neuromorphic-paris/hibiscus/parts/box/ethernet.stl

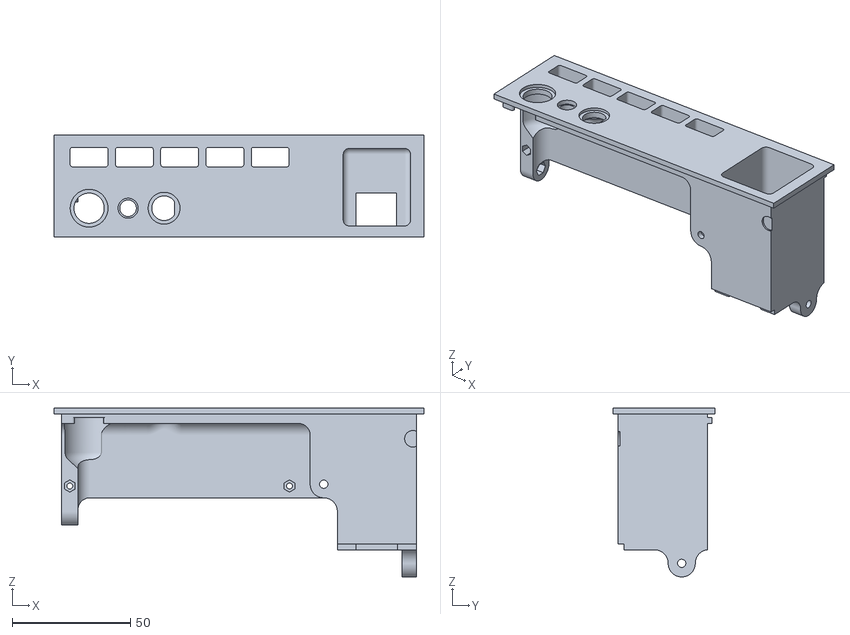
[picture p18: CAD file, 2019-12-23]
parts/box/ethernet.stl
156.7 x 43.2 x 71.5
