neuromorphic-paris/hibiscus/parts/box/slider.stl

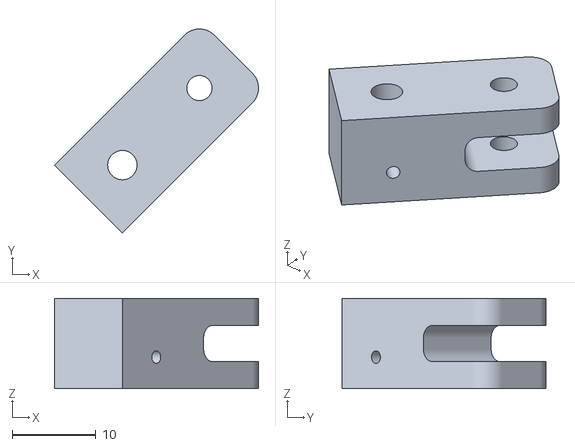
[picture p19: CAD file, 2019-12-23]
parts/box/slider.stl
24.3 x 24.3 x 10.7
