neuromorphic-paris/hibiscus/parts/box/antenna_spacer.stl

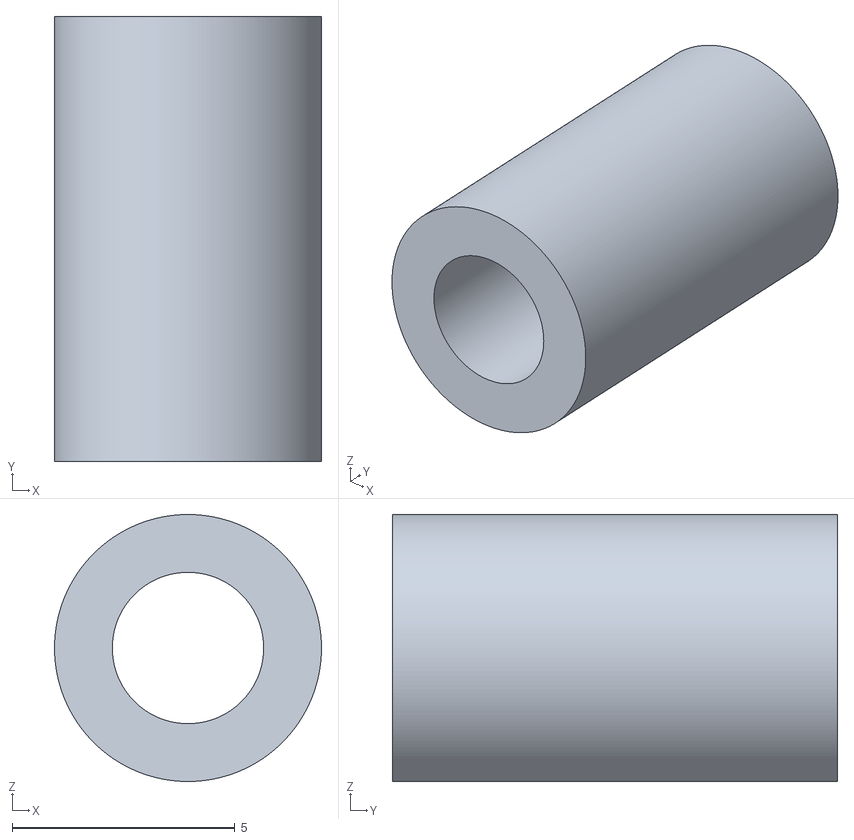
[picture p20: CAD file, 2019-12-23]
parts/box/antenna_spacer.stl
6.00 x 10.0 x 6.00
