neuromorphic-paris/hibiscus/parts/box/chassis.stl

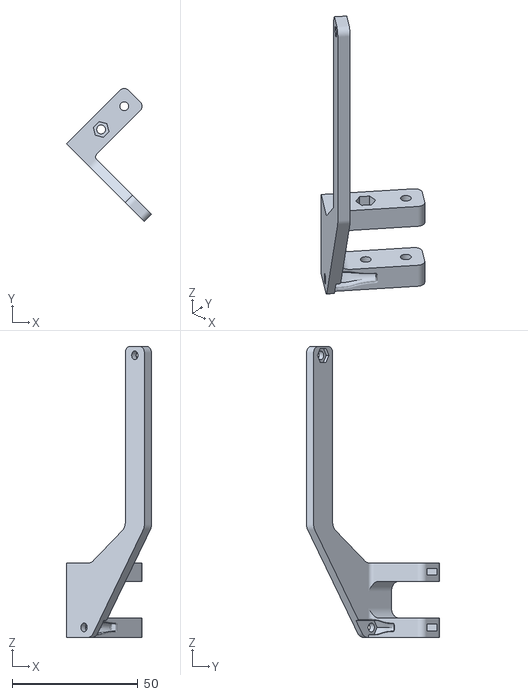
[picture p21: CAD file, 2019-12-23]
parts/box/chassis.stl
33.7 x 52.8 x 115.5
