neuromorphic-paris/hibiscus/parts/box/teensee_holder.stl

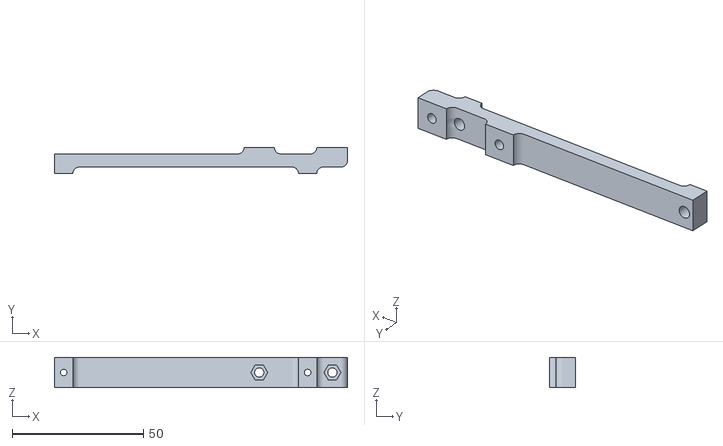
[picture p22: CAD file, 2019-12-23]
parts/box/teensee_holder.stl
111.7 x 10.00 x 11.5
